monmorera/Bluetooth-RC-Car/SolidWorks/3D print parts of car/PCBsupportV3.STL

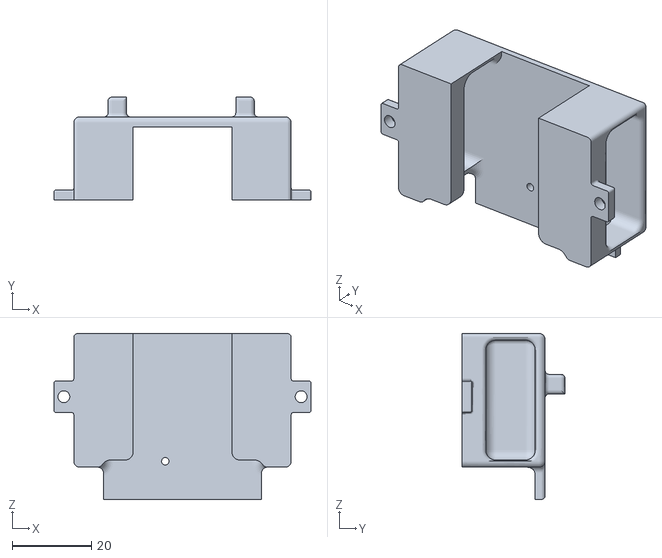
[picture p23: CAD file, 2019-11-09]
SolidWorks/3D print parts of car/PCBsupportV3.STL
65.0 x 26.0 x 42.0
