monmorera/Bluetooth-RC-Car/SolidWorks/AddOn_model_parts/joy_stick_BTRC.SLDPRT

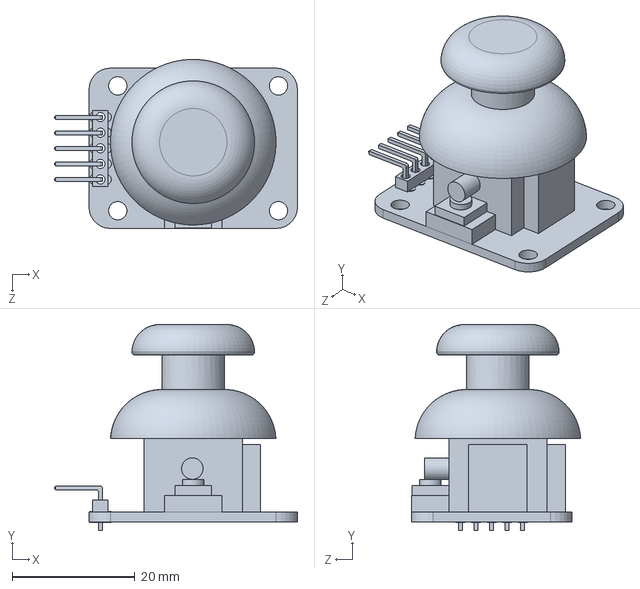
[picture p24: CAD file, 2019-11-09]
SolidWorks/AddOn_model_parts/joy_stick_BTRC.SLDPRT
39.6 x 33.6 x 27.6 mm
