monmorera/Bluetooth-RC-Car/SolidWorks/3D print parts of car/motorMountV2.STL

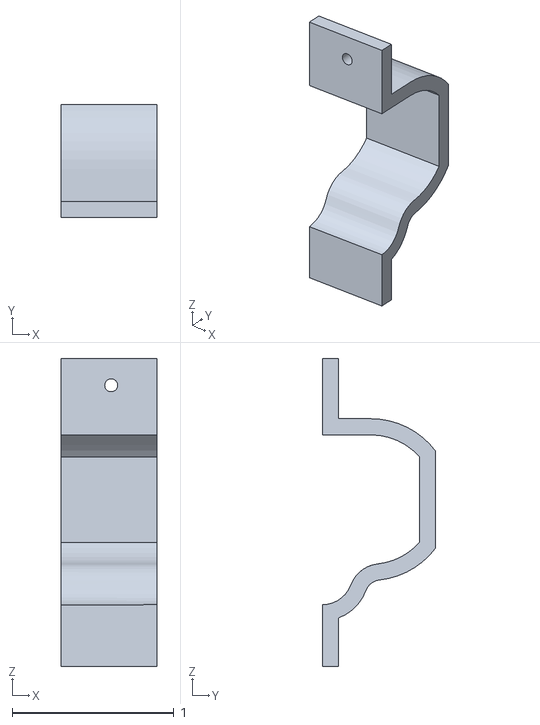
[picture p25: CAD file, 2019-11-09]
SolidWorks/3D print parts of car/motorMountV2.STL
0.594 x 0.7 x 1.90
