monmorera/Bluetooth-RC-Car/SolidWorks/AddOn_model_parts/micro_servo_arm.SLDPRT

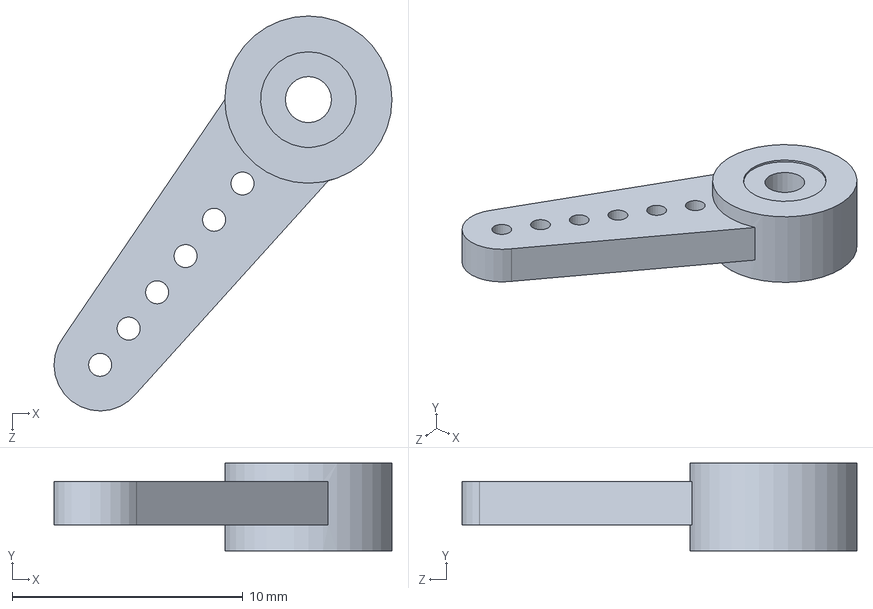
[picture p26: CAD file, 2019-11-09]
SolidWorks/AddOn_model_parts/micro_servo_arm.SLDPRT
14.7 x 3.80 x 17.1 mm
