monmorera/Bluetooth-RC-Car/SolidWorks/3D print parts of car/FrontFlexConnectorV1.STL

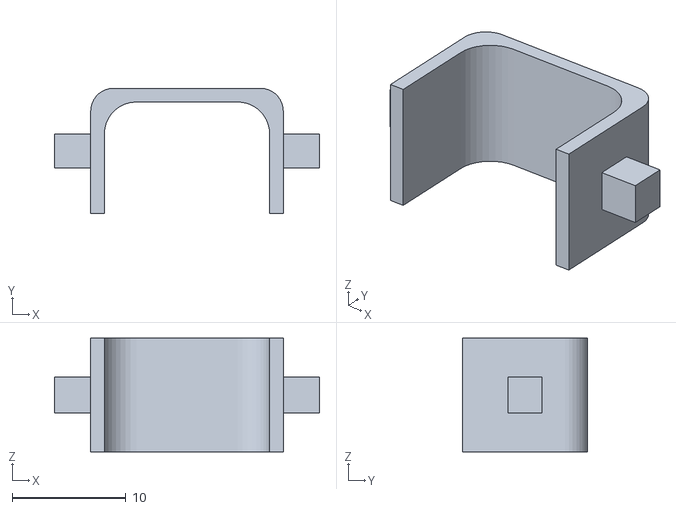
[picture p27: CAD file, 2019-11-09]
SolidWorks/3D print parts of car/FrontFlexConnectorV1.STL
23.2 x 11.0 x 10.0
