monmorera/Bluetooth-RC-Car/SolidWorks/AddOn_model_parts/BTRC DC motor.SLDPRT

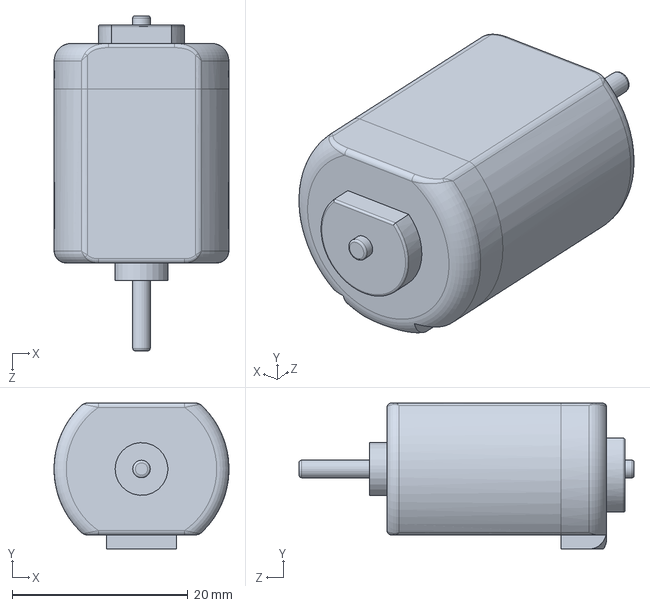
[picture p28: CAD file, 2019-11-09]
SolidWorks/AddOn_model_parts/BTRC DC motor.SLDPRT
19.9 x 16.6 x 38.1 mm
