monmorera/Bluetooth-RC-Car/SolidWorks/3D print parts of car/BackWheelV7.STL

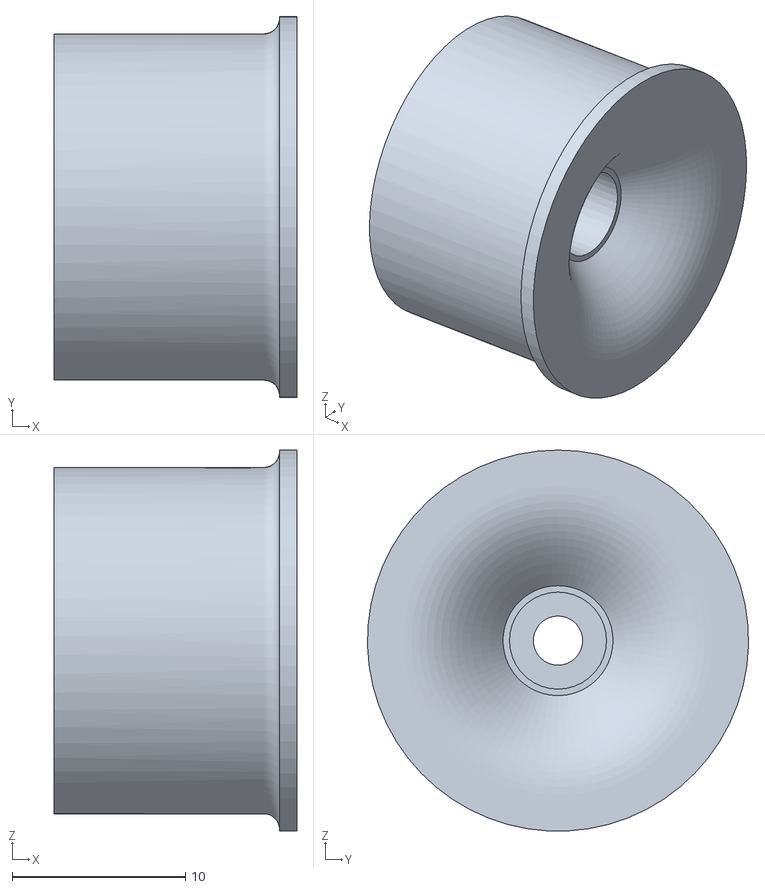
[picture p29: CAD file, 2019-11-09]
SolidWorks/3D print parts of car/BackWheelV7.STL
14.0 x 22.0 x 22.0
