monmorera/Bluetooth-RC-Car/SolidWorks/AddOn_model_parts/Buu tire v2.SLDPRT

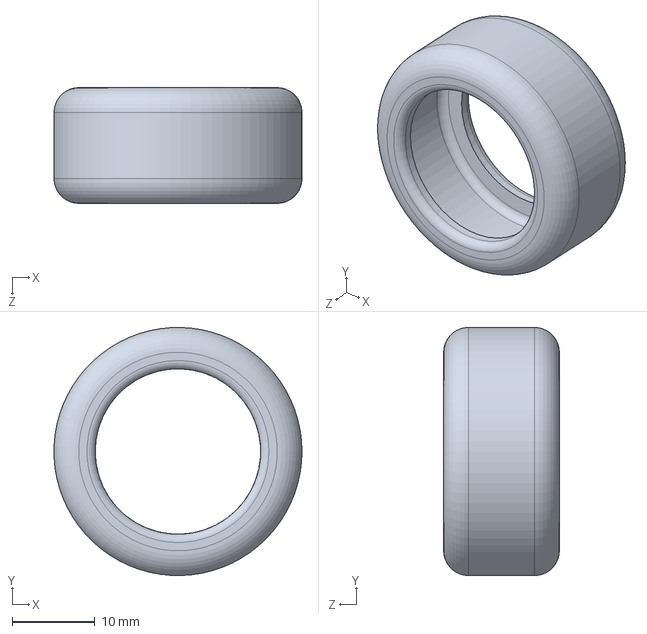
[picture p30: CAD file, 2019-11-09]
SolidWorks/AddOn_model_parts/Buu tire v2.SLDPRT
30.0 x 30.0 x 14.0 mm
