monmorera/Bluetooth-RC-Car/SolidWorks/AddOn_model_parts/Servo-MG90S.SLDPRT

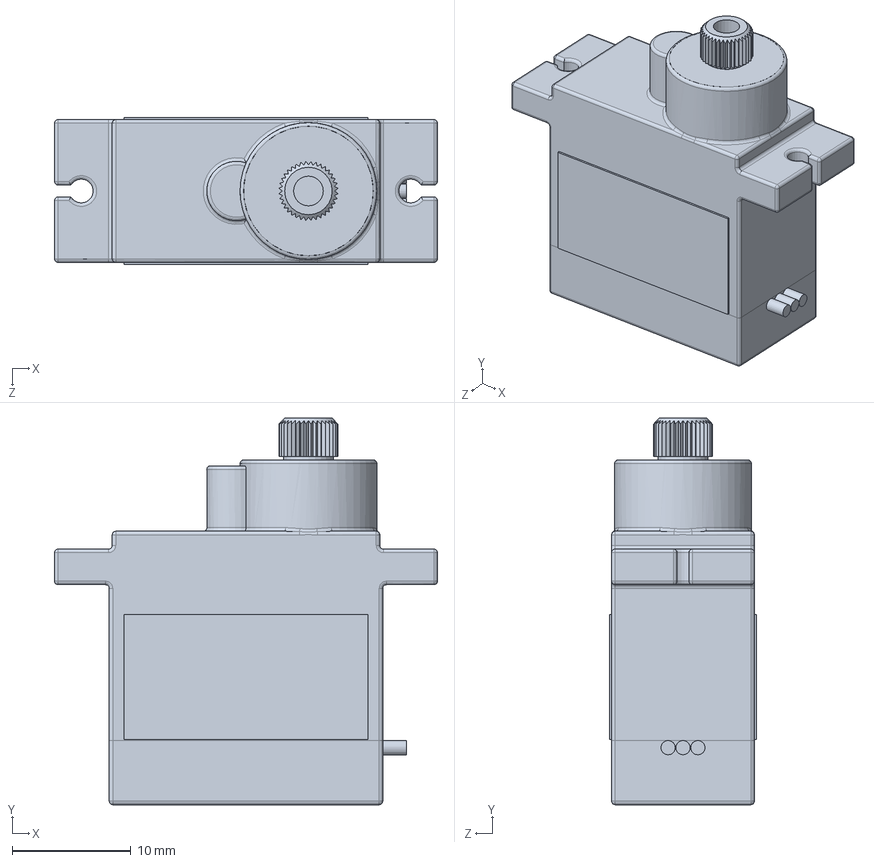
[picture p31: CAD file, 2019-11-09]
SolidWorks/AddOn_model_parts/Servo-MG90S.SLDPRT
32.2 x 32.5 x 12.4 mm
